lewesche/RC_Car/CAD/Solidworks Parts/Rear_Axle_Mount.SLDPRT

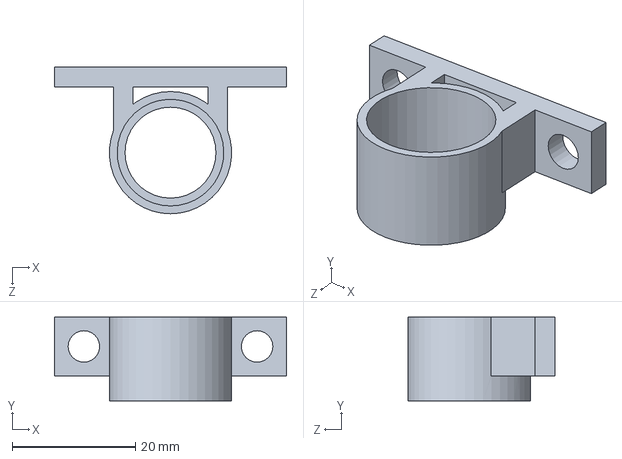
[picture p15: CAD file, 2019-04-11]
CAD/Solidworks Parts/Rear_Axle_Mount.SLDPRT
37.6 x 13.6 x 23.7 mm
