lewesche/RC_Car/CAD/Solidworks Parts/MG90S_Servo.SLDPRT

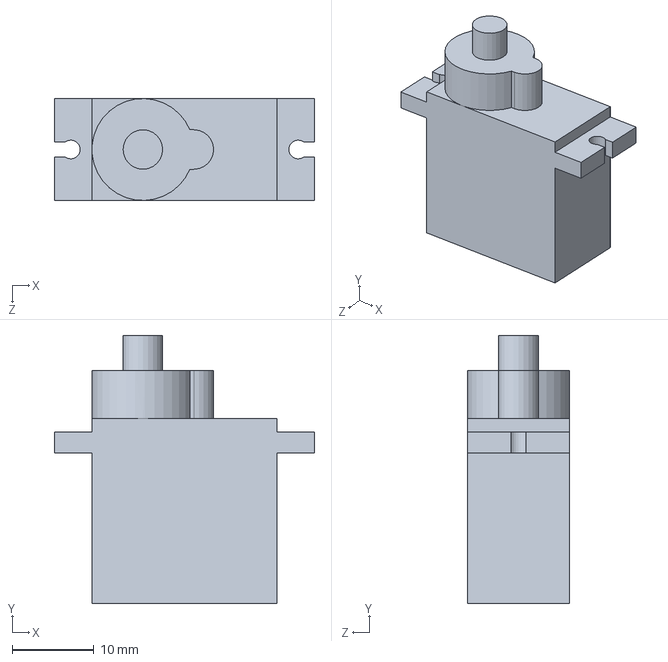
[picture p16: CAD file, 2019-04-11]
CAD/Solidworks Parts/MG90S_Servo.SLDPRT
31.8 x 32.8 x 12.4 mm
