lewesche/RC_Car/CAD/Solidworks Parts/Steering_Mount.SLDPRT

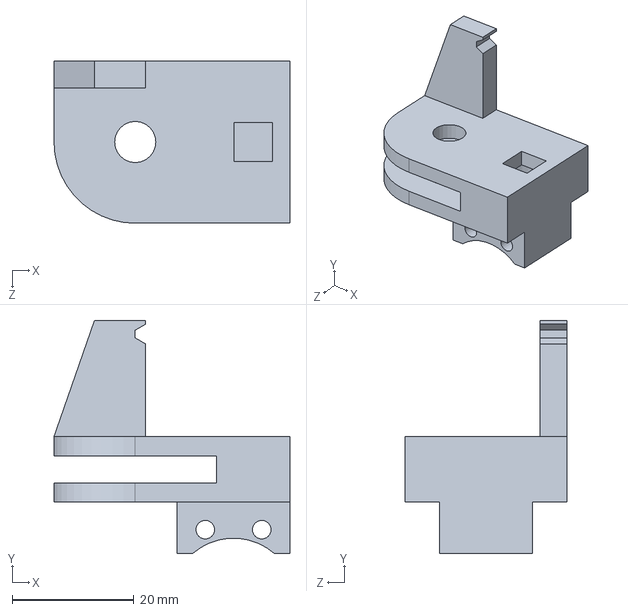
[picture p17: CAD file, 2019-04-11]
CAD/Solidworks Parts/Steering_Mount.SLDPRT
38.7 x 38.3 x 26.7 mm
