lewesche/RC_Car/CAD/Solidworks Parts/Motor_Rod.SLDPRT

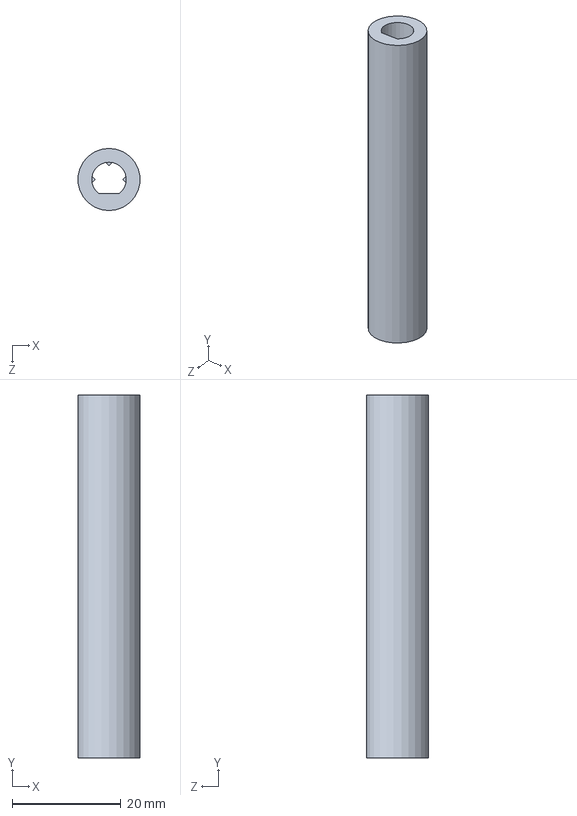
[picture p18: CAD file, 2019-04-11]
CAD/Solidworks Parts/Motor_Rod.SLDPRT
11.3 x 66.7 x 11.4 mm
