lewesche/RC_Car/CAD/Solidworks Parts/Driveshaft.SLDPRT

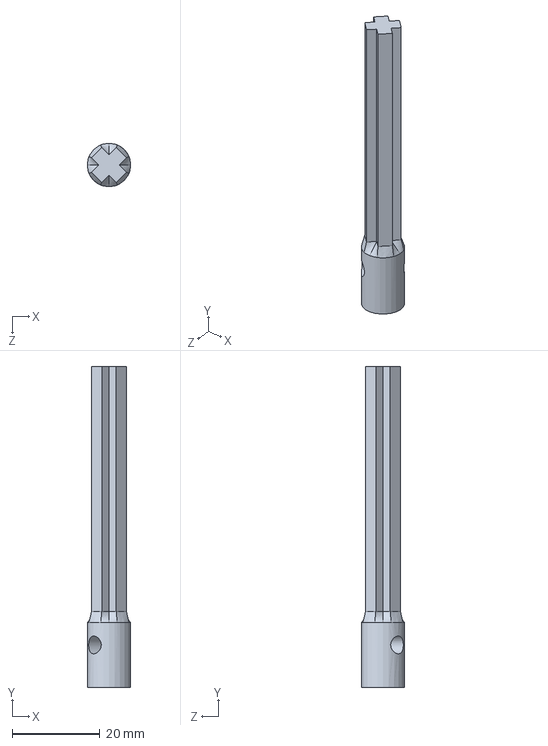
[picture p19: CAD file, 2019-04-11]
CAD/Solidworks Parts/Driveshaft.SLDPRT
9.91 x 73.2 x 9.91 mm
