lewesche/RC_Car/CAD/Solidworks Parts/Servo_Attachment_2.SLDPRT

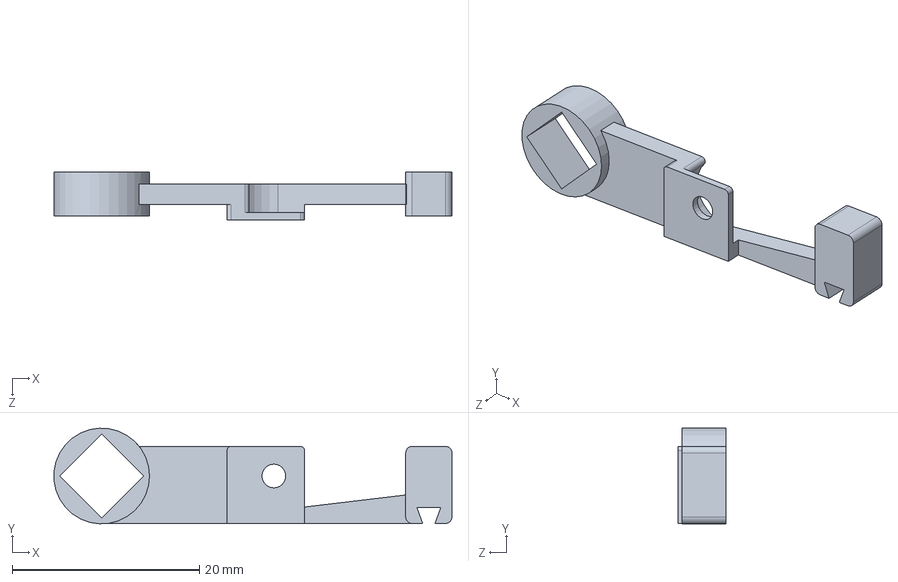
[picture p20: CAD file, 2019-04-11]
CAD/Solidworks Parts/Servo_Attachment_2.SLDPRT
42.6 x 10.2 x 5.08 mm
