lewesche/RC_Car/CAD/Solidworks Parts/Bevel_Gear_3.SLDPRT

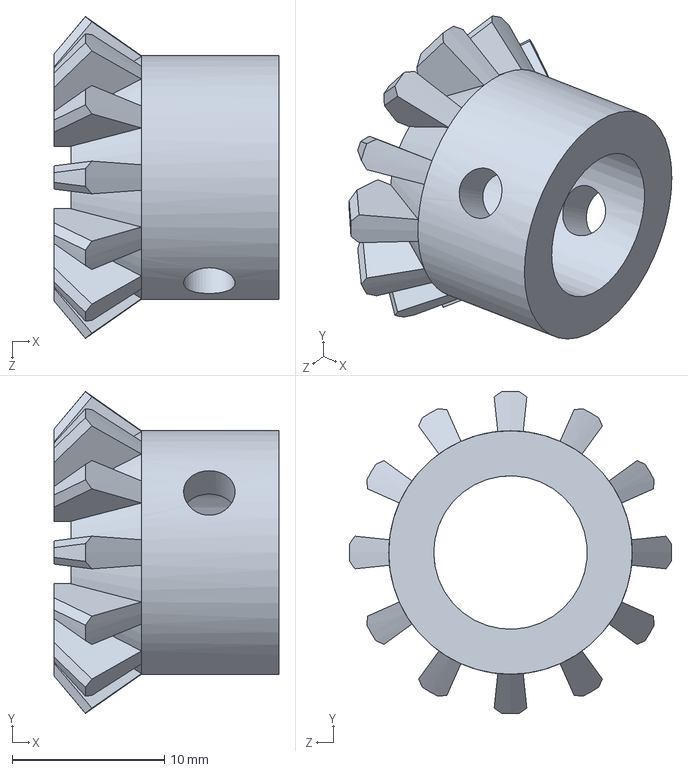
[picture p21: CAD file, 2019-04-11]
CAD/Solidworks Parts/Bevel_Gear_3.SLDPRT
14.8 x 21.2 x 21.2 mm
