lewesche/RC_Car/CAD/Solidworks Parts/Steering_Mount_Right.SLDPRT

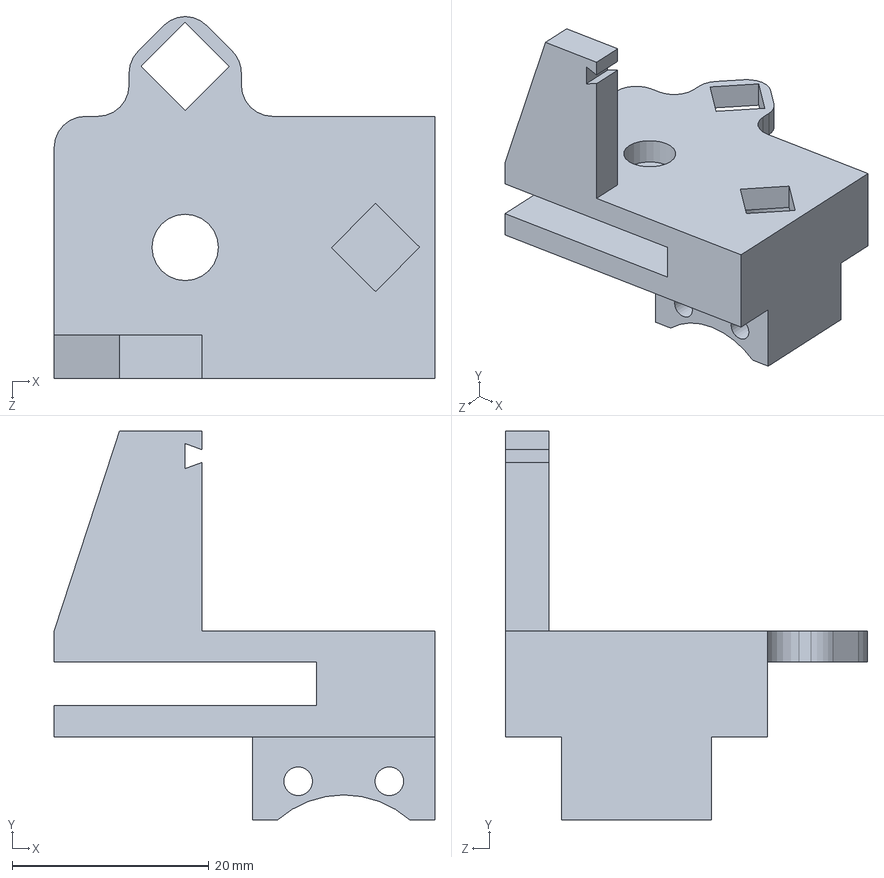
[picture p22: CAD file, 2019-04-11]
CAD/Solidworks Parts/Steering_Mount_Right.SLDPRT
38.7 x 39.6 x 36.8 mm
