lewesche/RC_Car/CAD/Solidworks Parts/Motor_Mount_Top.SLDPRT

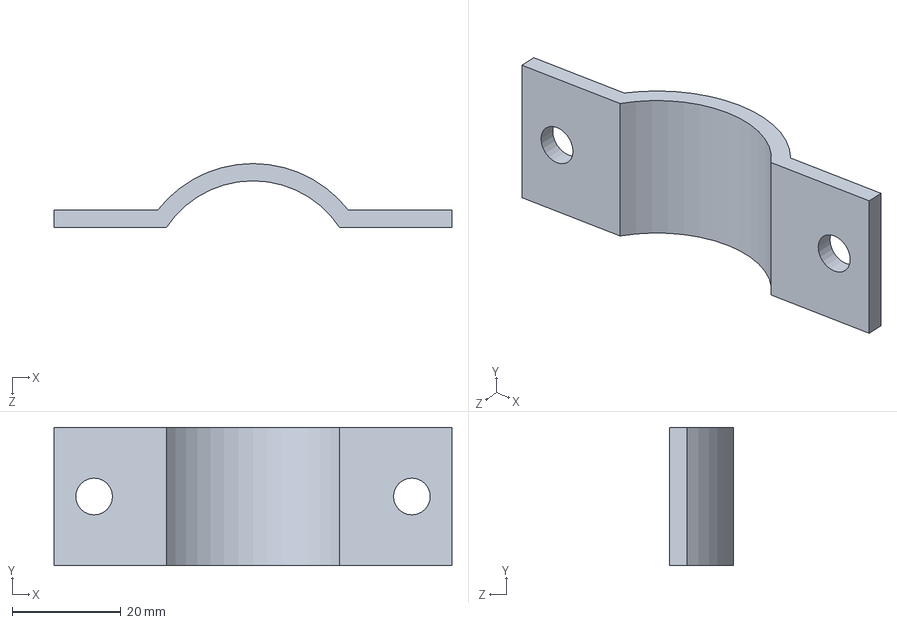
[picture p23: CAD file, 2019-04-11]
CAD/Solidworks Parts/Motor_Mount_Top.SLDPRT
73.2 x 25.4 x 11.7 mm
