lewesche/RC_Car/CAD/Solidworks Parts/Arduino UNO.SLDPRT

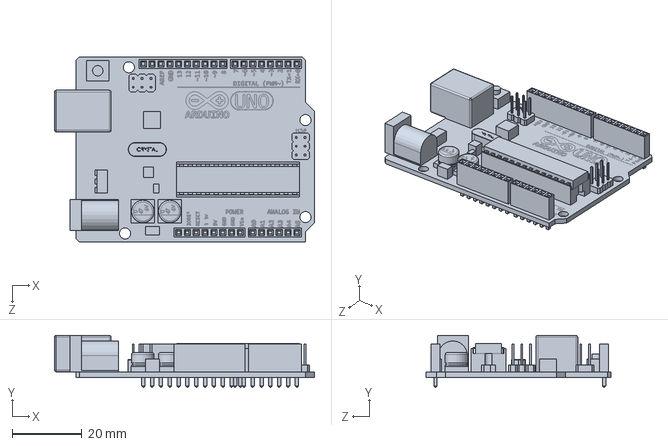
[picture p24: CAD file, 2019-04-11]
CAD/Solidworks Parts/Arduino UNO.SLDPRT
74.8 x 15.1 x 53.3 mm
