lewesche/RC_Car/CAD/Solidworks Parts/Plate.SLDPRT

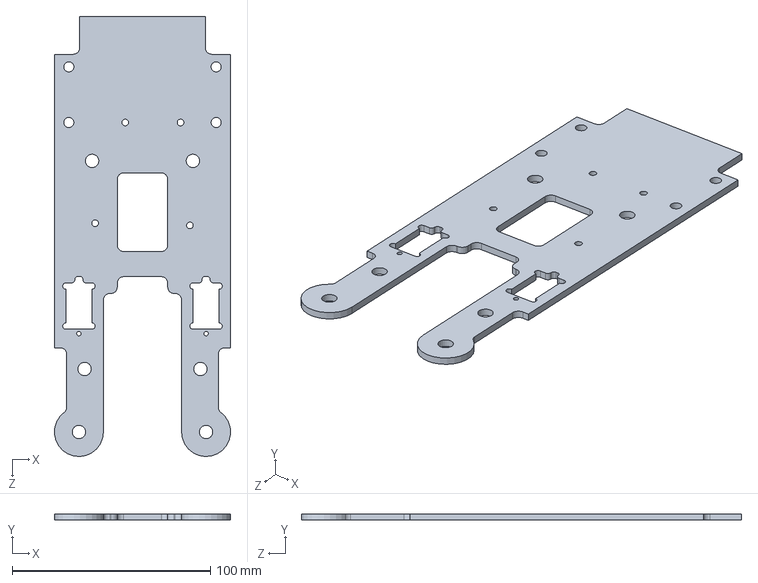
[picture p25: CAD file, 2019-04-11]
CAD/Solidworks Parts/Plate.SLDPRT
88.9 x 3.17 x 221.9 mm
