lewesche/RC_Car/CAD/Solidworks Parts/Gear_Test_Fit.SLDPRT

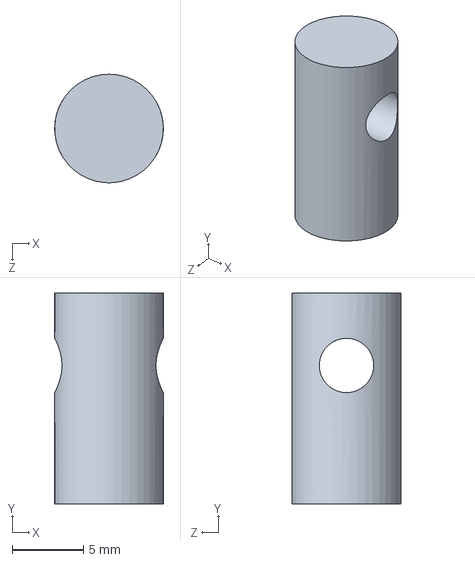
[picture p26: CAD file, 2018-07-14]
CAD/Solidworks Parts/Gear_Test_Fit.SLDPRT
7.62 x 14.8 x 7.62 mm
