lewesche/RC_Car/CAD/Solidworks Parts/RC_Plate.DXF

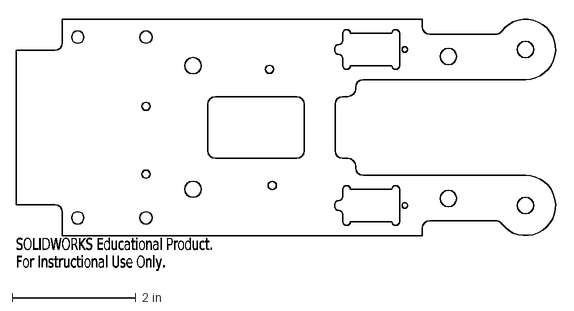
[picture p27: CAD file, 2018-07-14]
CAD/Solidworks Parts/RC_Plate.DXF
SOLIDWORKS Educational Product.
For Instructional Use Only.
