lewesche/RC_Car/CAD/Solidworks Parts/Rear_Wheel.SLDPRT

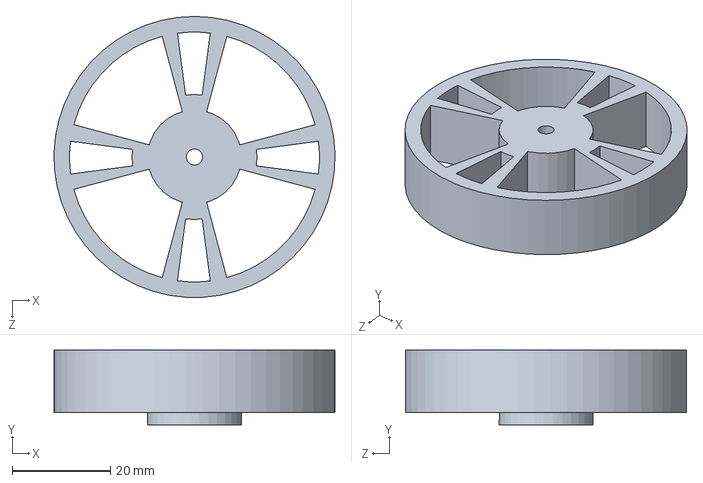
[picture p28: CAD file, 2018-07-06]
CAD/Solidworks Parts/Rear_Wheel.SLDPRT
57.1 x 15.2 x 57.1 mm
