lewesche/RC_Car/CAD/Solidworks Parts/Front_Wheel.SLDPRT

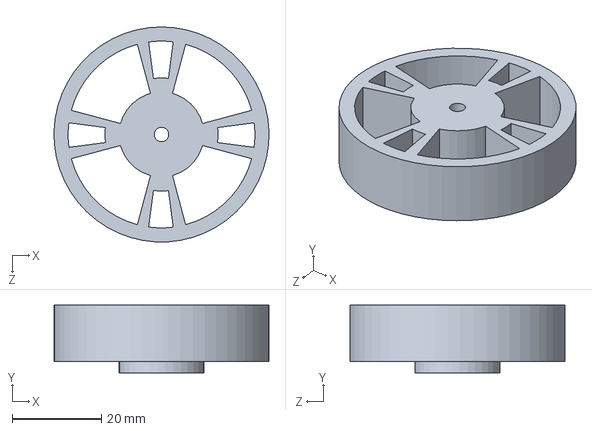
[picture p29: CAD file, 2018-07-06]
CAD/Solidworks Parts/Front_Wheel.SLDPRT
48.2 x 15.2 x 48.3 mm
