lewesche/RC_Car/CAD/Solidworks Parts/Bevel_Gear_2.SLDPRT

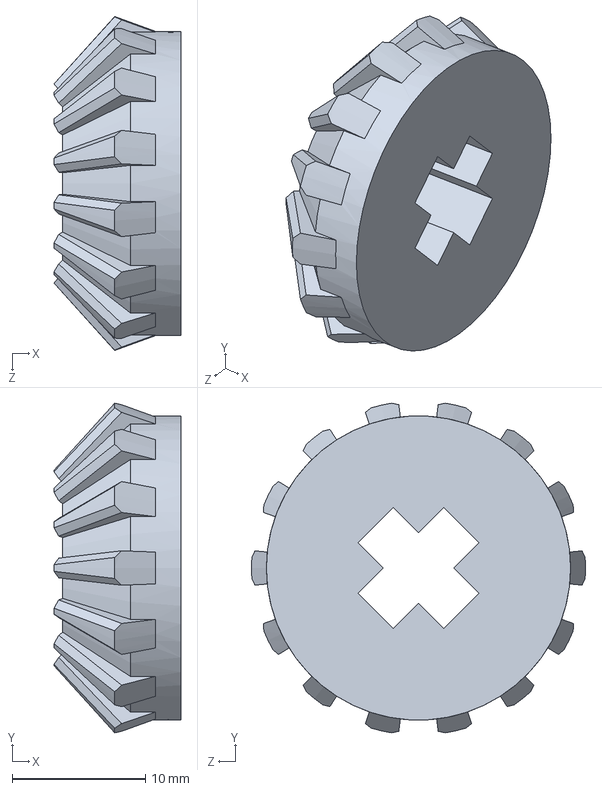
[picture p30: CAD file, 2018-06-25]
CAD/Solidworks Parts/Bevel_Gear_2.SLDPRT
9.54 x 24.8 x 25.1 mm
