lewesche/RC_Car/CAD/Solidworks Parts/Test_Fit_4.SLDPRT

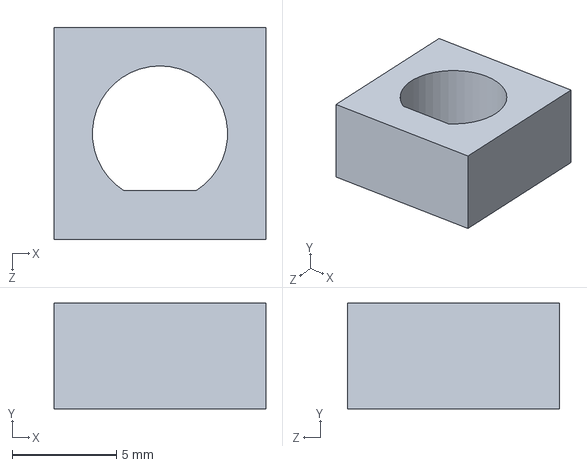
[picture p31: CAD file, 2018-06-20]
CAD/Solidworks Parts/Test_Fit_4.SLDPRT
10.2 x 5.08 x 10.2 mm
